Tynashe28/IIOT_Industrial_interface_controller/images/1.PNG

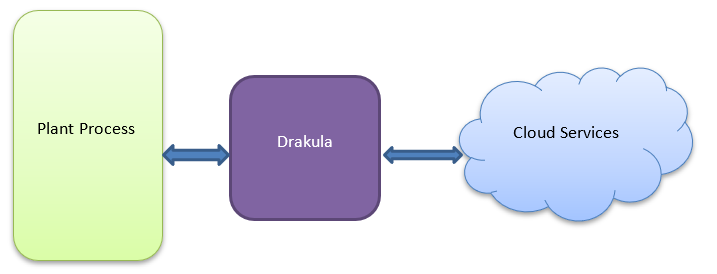
images/1.PNG
