Tynashe28/IIOT_Industrial_interface_controller/images/2.PNG

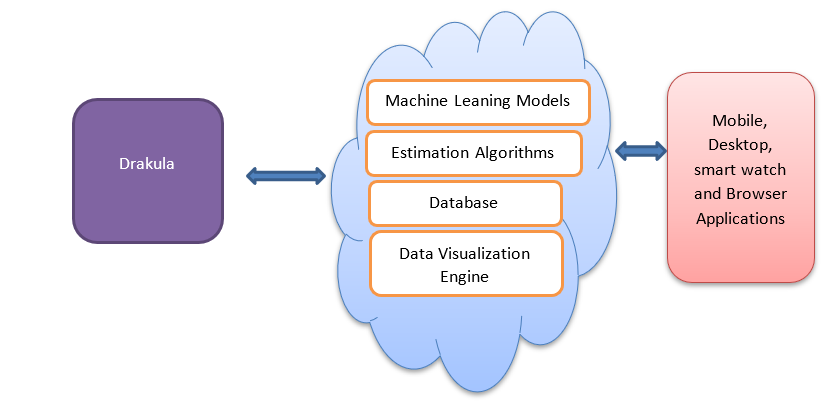
images/2.PNG
