Tynashe28/IIOT_Industrial_interface_controller/images/3.PNG

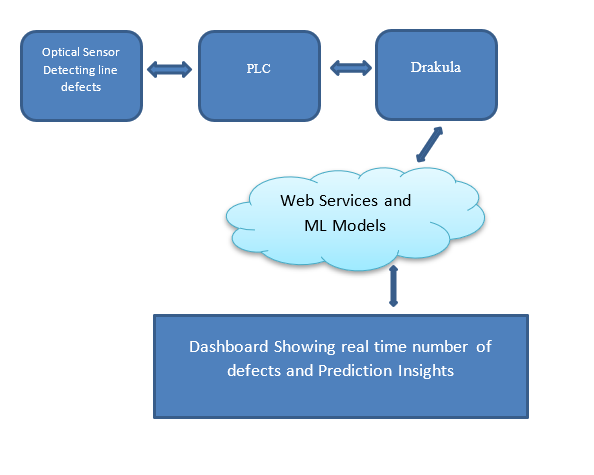
images/3.PNG
