Tynashe28/IIOT_Industrial_interface_controller/images/4.PNG

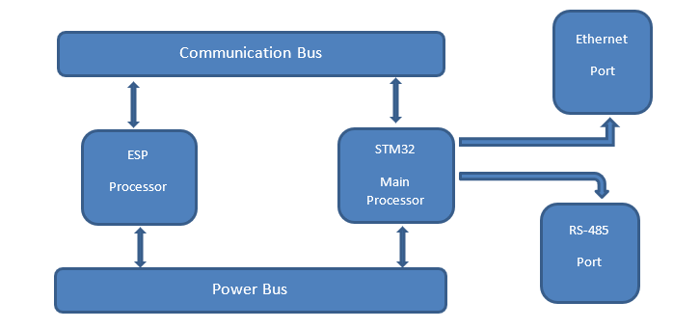
images/4.PNG
